emeb/ESP32S2_Audio/Firmware/main/esp_gfx.c

/*
 * esp_gfx.c - ST7735 graphics using the ESP built-in graphics driver
 * 03-05-22 E. Brombaugh
 */

#include <stdio.h>
#include "main.h"
#include "esp_lcd_panel_io.h"
#include "esp_lcd_panel_vendor.h"
#include "esp_lcd_panel_ops.h"
#include "driver/gpio.h"
#include "driver/spi_master.h"
#include "esp_err.h"
#include "esp_log.h"
#include "lvgl.h"
#include "esp_gfx.h"

// Using SPI2 in the example
#define LCD_HOST  SPI2_HOST

////////////////////////////////////////////////////////////////////////////////////////////////////////////////////////
//////////////////// Please update the following configuration according to your LCD spec //////////////////////////////
////////////////////////////////////////////////////////////////////////////////////////////////////////////////////////
#define EXAMPLE_LCD_PIXEL_CLOCK_HZ     (20 * 1000 * 1000)
#define EXAMPLE_LCD_BK_LIGHT_ON_LEVEL  1
#define EXAMPLE_LCD_BK_LIGHT_OFF_LEVEL !EXAMPLE_LCD_BK_LIGHT_ON_LEVEL
#define EXAMPLE_PIN_NUM_DATA0          34
#define EXAMPLE_PIN_NUM_PCLK           33
#define EXAMPLE_PIN_NUM_CS             37
#define EXAMPLE_PIN_NUM_DC             36
#define EXAMPLE_PIN_NUM_RST            35
#define EXAMPLE_PIN_NUM_BK_LIGHT       38

// The pixel number in horizontal and vertical
#define EXAMPLE_LCD_H_RES              160
#define EXAMPLE_LCD_V_RES              80
// Bit number used to represent command and parameter
#define EXAMPLE_LCD_CMD_BITS           8
#define EXAMPLE_LCD_PARAM_BITS         8

#define EXAMPLE_LVGL_TICK_PERIOD_MS    2

static const char* TAG = "esp_gfx";

/*
 * helpers
 */
static bool example_notify_lvgl_flush_ready(esp_lcd_panel_io_handle_t panel_io, esp_lcd_panel_io_event_data_t *edata, void *user_ctx)
{
    lv_disp_drv_t *disp_driver = (lv_disp_drv_t *)user_ctx;
    lv_disp_flush_ready(disp_driver);
    return false;
}

static void example_lvgl_flush_cb(lv_disp_drv_t *drv, const lv_area_t *area, lv_color_t *color_map)
{
    esp_lcd_panel_handle_t panel_handle = (esp_lcd_panel_handle_t) drv->user_data;
    int offsetx1 = area->x1;
    int offsetx2 = area->x2;
    int offsety1 = area->y1;
    int offsety2 = area->y2;
    // copy a buffer's content to a specific area of the display
    esp_lcd_panel_draw_bitmap(panel_handle, offsetx1, offsety1, offsetx2 + 1, offsety2 + 1, color_map);
}

static void example_increase_lvgl_tick(void *arg)
{
    /* Tell LVGL how many milliseconds has elapsed */
    lv_tick_inc(EXAMPLE_LVGL_TICK_PERIOD_MS);
}

static lv_obj_t *arc1, *arc2;
static lv_obj_t *label1, *label2;

void example_lvgl_demo_ui(lv_obj_t *scr)
{
    arc1 = lv_arc_create(lv_scr_act());
    lv_obj_set_size(arc1, 60, 60);
    lv_arc_set_rotation(arc1, 135);
    lv_arc_set_bg_angles(arc1, 0, 270);
	lv_obj_set_pos(arc1, 10, 10);
	lv_obj_remove_style(arc1, NULL, LV_PART_KNOB);
	lv_obj_clear_flag(arc1, LV_OBJ_FLAG_CLICKABLE);
	
    arc2 = lv_arc_create(lv_scr_act());
    lv_obj_set_size(arc2, 60, 60);
    lv_arc_set_rotation(arc2, 135);
    lv_arc_set_bg_angles(arc2, 0, 270);
	lv_obj_set_pos(arc2, 90, 10);
	lv_obj_remove_style(arc2, NULL, LV_PART_KNOB);
	lv_obj_clear_flag(arc2, LV_OBJ_FLAG_CLICKABLE);
	
	label1 = lv_label_create(lv_scr_act());
	lv_obj_set_parent(label1, arc1);
	lv_label_set_long_mode(label1, LV_LABEL_LONG_WRAP);     /*Break the long lines*/
    lv_label_set_recolor(label1, true);                      /*Enable re-coloring by commands in the text*/
    lv_obj_set_width(label1, 48);  /*Set smaller width to make the lines wrap*/
    lv_obj_set_style_text_align(label1, LV_TEXT_ALIGN_CENTER, 0);
    lv_obj_align(label1, LV_ALIGN_CENTER, 0, -40);
	lv_label_set_text(label1, "0");
	lv_obj_center(label1);

	label2 = lv_label_create(lv_scr_act());
	lv_obj_set_parent(label2, arc2);
	lv_label_set_long_mode(label2, LV_LABEL_LONG_WRAP);     /*Break the long lines*/
    lv_label_set_recolor(label2, true);                      /*Enable re-coloring by commands in the text*/
    lv_obj_set_width(label2, 48);  /*Set smaller width to make the lines wrap*/
    lv_obj_set_style_text_align(label2, LV_TEXT_ALIGN_CENTER, 0);
    lv_obj_align(label2, LV_ALIGN_CENTER, 0, -40);
	lv_label_set_text(label2, "0");
	lv_obj_center(label2);
}

/*
 * initialize the interface
 */
esp_err_t esp_gfx_init(void)
{
    static lv_disp_draw_buf_t disp_buf; // contains internal graphic buffer(s) called draw buffer(s)
    static lv_disp_drv_t disp_drv;      // contains callback functions

    ESP_LOGI(TAG, "Turn off LCD backlight");
    gpio_config_t bk_gpio_config = {
        .mode = GPIO_MODE_OUTPUT,
        .pin_bit_mask = 1ULL << EXAMPLE_PIN_NUM_BK_LIGHT
    };
    ESP_ERROR_CHECK(gpio_config(&bk_gpio_config));

    ESP_LOGI(TAG, "Initialize SPI bus");
    spi_bus_config_t buscfg = {
        .sclk_io_num = EXAMPLE_PIN_NUM_PCLK,
        .mosi_io_num = EXAMPLE_PIN_NUM_DATA0,
        .miso_io_num = -1,
        .quadwp_io_num = -1,
        .quadhd_io_num = -1,
        .max_transfer_sz = EXAMPLE_LCD_H_RES * 80 * sizeof(uint16_t),
    };
    ESP_ERROR_CHECK(spi_bus_initialize(LCD_HOST, &buscfg, SPI_DMA_CH_AUTO));

    ESP_LOGI(TAG, "Install panel IO");
    esp_lcd_panel_io_handle_t io_handle = NULL;
    esp_lcd_panel_io_spi_config_t io_config = {
        .dc_gpio_num = EXAMPLE_PIN_NUM_DC,
        .cs_gpio_num = EXAMPLE_PIN_NUM_CS,
        .pclk_hz = EXAMPLE_LCD_PIXEL_CLOCK_HZ,
        .lcd_cmd_bits = EXAMPLE_LCD_CMD_BITS,
        .lcd_param_bits = EXAMPLE_LCD_PARAM_BITS,
        .spi_mode = 0,
        .trans_queue_depth = 10,
        .on_color_trans_done = example_notify_lvgl_flush_ready,
        .user_ctx = &disp_drv,
    };
    // Attach the LCD to the SPI bus
    ESP_ERROR_CHECK(esp_lcd_new_panel_io_spi((esp_lcd_spi_bus_handle_t)LCD_HOST, &io_config, &io_handle));

    ESP_LOGI(TAG, "Install ST7735/ST7789 panel driver");
    esp_lcd_panel_handle_t panel_handle = NULL;
    esp_lcd_panel_dev_config_t panel_config = {
        .reset_gpio_num = EXAMPLE_PIN_NUM_RST,
        .color_space = ESP_LCD_COLOR_SPACE_BGR,
        .bits_per_pixel = 16,
    };
    ESP_ERROR_CHECK(esp_lcd_new_panel_st7789(io_handle, &panel_config, &panel_handle));

    ESP_ERROR_CHECK(esp_lcd_panel_reset(panel_handle));
    ESP_ERROR_CHECK(esp_lcd_panel_init(panel_handle));
	ESP_ERROR_CHECK(esp_lcd_panel_set_gap(panel_handle, 0, 24));
    ESP_ERROR_CHECK(esp_lcd_panel_mirror(panel_handle, true, false));
    ESP_ERROR_CHECK(esp_lcd_panel_swap_xy(panel_handle, true));
	
    ESP_LOGI(TAG, "Turn on LCD backlight");
    gpio_set_level(EXAMPLE_PIN_NUM_BK_LIGHT, EXAMPLE_LCD_BK_LIGHT_ON_LEVEL);

    ESP_LOGI(TAG, "Initialize LVGL library");
    lv_init();
    // alloc draw buffers used by LVGL
    // it's recommended to choose the size of the draw buffer(s) to be at least 1/10 screen sized
    lv_color_t *buf1 = heap_caps_malloc(EXAMPLE_LCD_H_RES * 20 * sizeof(lv_color_t), MALLOC_CAP_DMA);
    assert(buf1);
    lv_color_t *buf2 = heap_caps_malloc(EXAMPLE_LCD_H_RES * 20 * sizeof(lv_color_t), MALLOC_CAP_DMA);
    assert(buf2);
    // initialize LVGL draw buffers
    lv_disp_draw_buf_init(&disp_buf, buf1, buf2, EXAMPLE_LCD_H_RES * 20);

    ESP_LOGI(TAG, "Register display driver to LVGL");
    lv_disp_drv_init(&disp_drv);
    disp_drv.hor_res = EXAMPLE_LCD_H_RES;
    disp_drv.ver_res = EXAMPLE_LCD_V_RES;
    disp_drv.flush_cb = example_lvgl_flush_cb;
    disp_drv.draw_buf = &disp_buf;
    disp_drv.user_data = panel_handle;
    lv_disp_t *disp = lv_disp_drv_register(&disp_drv);

    ESP_LOGI(TAG, "Install LVGL tick timer");
    // Tick interface for LVGL (using esp_timer to generate 2ms periodic event)
    const esp_timer_create_args_t lvgl_tick_timer_args = {
        .callback = &example_increase_lvgl_tick,
        .name = "lvgl_tick"
    };
    esp_timer_handle_t lvgl_tick_timer = NULL;
    ESP_ERROR_CHECK(esp_timer_create(&lvgl_tick_timer_args, &lvgl_tick_timer));
    ESP_ERROR_CHECK(esp_timer_start_periodic(lvgl_tick_timer, EXAMPLE_LVGL_TICK_PERIOD_MS * 1000));

    ESP_LOGI(TAG, "Start Demo");
    lv_obj_t *scr = lv_disp_get_scr_act(disp);
    example_lvgl_demo_ui(scr);
	
	return ESP_OK;
}

/*
 * update the graphics
 */
void esp_gfx_update(int16_t *v)
{
	// The task running lv_timer_handler should have lower priority than that running `lv_tick_inc`
	lv_timer_handler();
	
	char txtbuf[6];
	int32_t value = v[1]/82;
    lv_arc_set_value(arc1, value);
    sprintf(txtbuf, "%3d", value);
	lv_label_set_text(label1, txtbuf);
	value = v[0]/82;
    lv_arc_set_value(arc2, value);
    sprintf(txtbuf, "%3d", value);
	lv_label_set_text(label2, txtbuf);
}
