emeb/ESP32S2_Audio/Firmware/main/audio.h

/*
 * audio.h - audio via I2S.
 * 03-9-22 E. Brombaugh
 */

#ifndef __audio__
#define __audio__

extern int16_t audio_sl[4];
extern uint64_t audio_load[3];
esp_err_t audio_init(void);
void audio_mute(uint8_t enable);

#endif
