emeb/ESP32S2_Audio/Firmware/main/fx.h

/*
 * fx.h - Algorithm access for esp32s2_audio
 * 03-13-22 E. Brombaugh
 */

#ifndef __fx__
#define __fx__

#include "main.h"
#include "dsp_lib.h"
#include "eb_adc.h"
#include "gfx.h"

#define SAMPLE_RATE     (48000)
#define FRAMESZ			(32)

#define FX_NUM_ALGOS  3
#define FX_MAX_PARAMS 3
#define FX_MAX_MEM (129*1024)

/* pre-allocated external memory */
extern int16_t *fx_ext_buffer;
extern size_t fx_ext_sz;

/*
 * structure containing algorithm access info
 */
typedef struct
{
	const char *name;
	uint8_t parms;
	const char **parm_names;
	void * (*init)(uint32_t *mem);
	void (*cleanup)(void *blk);
	void (*proc)(void *blk, int16_t *dst, int16_t *src, uint16_t sz);
	void (*render_parm)(void *blk, uint8_t idx);
} fx_struct;

void fx_bypass_Cleanup(void *dummy);
void fx_bypass_Render_Parm(void *blk, uint8_t idx);

void fx_init(void);
void fx_select_algo(uint8_t algo);
void fx_proc(int16_t *dst, int16_t *src, uint16_t sz);
uint8_t fx_get_algo(void);
uint8_t fx_get_num_parms(void);
char * fx_get_algo_name(void);
char * fx_get_parm_name(uint8_t idx);
void fx_render_parm(uint8_t idx);

#endif
